flozenstein/rpi-pico2-simpanel/v2/boot.py

"""JoystickXL standard boot.py."""

import usb_hid  # type: ignore (this is a CircuitPython built-in)
from joystick_xl.hid import create_joystick

# This will enable all of the standard CircuitPython USB HID devices along with a
# USB HID joystick.
usb_hid.enable(
    (
        usb_hid.Device.KEYBOARD,
        usb_hid.Device.MOUSE,
        usb_hid.Device.CONSUMER_CONTROL,
        create_joystick(axes=2, buttons=24, hats=0),
    )
)
